mcanet/knitic/pcb_design/ArduinoDue_2.0_power_jumper_Vin_Arduino/KniticV201_+CompactPCB2Res_etch_silk_bottom.pdf

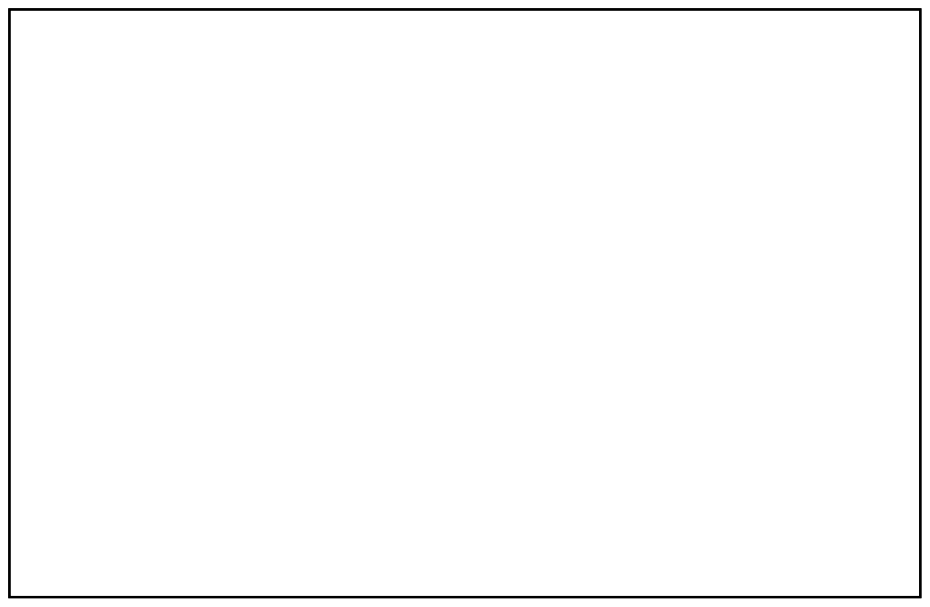
[picture p16: page 1]
