mcanet/knitic/pcb_design/ArduinoDue_2.0_power_jumper_Vin_Arduino/KniticV201_+CompactPCB2Res_etch_silk_bottom_mirror.pdf

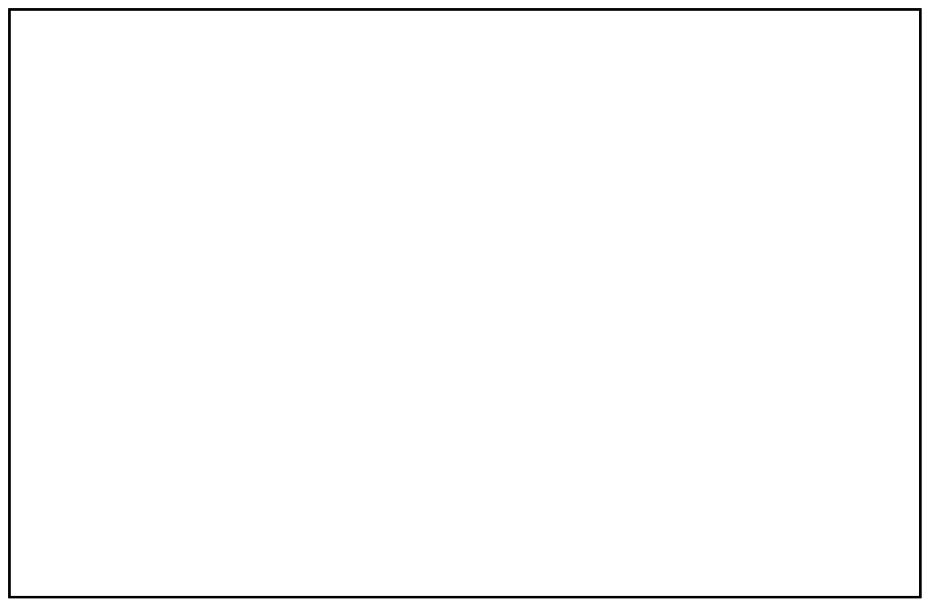
[picture p17: page 1]
