mcanet/knitic/pcb_design/ArduinoDue_2.0_power_jumper_Vin_Arduino/KniticV201_+CompactPCB2Res_etch_silk_top.pdf

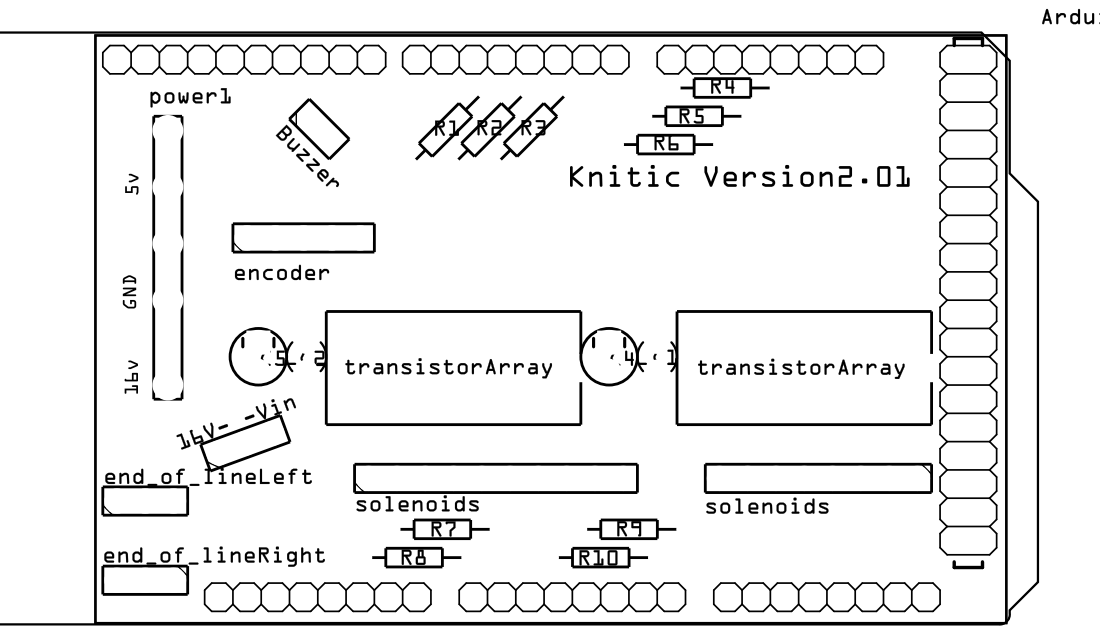
[picture p18: page 1]
