mcanet/knitic/pcb_design/ArduinoUno/KniticV1_pcb.pdf

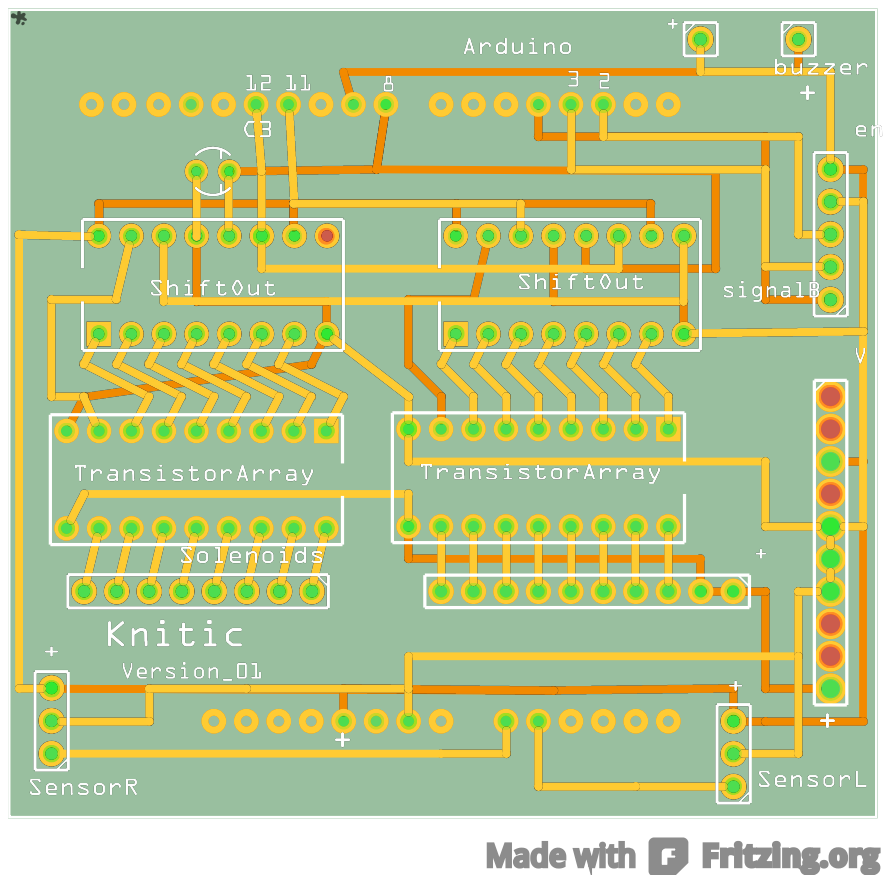
[picture p20: page 1]
