mcanet/knitic/arduino_code/openKnitting_handMadepcb_v0_1/communication.h

#ifndef COMMUNICATION_H_
#define COMMUNICATION_H_

#include "arduino.h"

#include "encoders.h"
#include "solenoids.h"
#include "endLines.h"

class communication {
  private:
    encoders* myEncoders;
    endLines* myEndlines;
    solenoids* mysolenoids;
    unsigned long lastSendTimeStamp;
    unsigned long lastRecieveTimeStamp;
    char receivedBin[202];
    int dataSize;
    boolean dataReplace;
    byte footer;
    char lf;
    boolean solenoidsAreOff;
    boolean corruptMessage;
    
  public:
    String _status;
    communication() {
    }
    ~communication() {
    }

    void setup(encoders* _myEncoders, endLines* _myEndlines, solenoids* _mysolenoids) {
      myEncoders = _myEncoders;
      myEndlines = _myEndlines;
      mysolenoids = _mysolenoids;
      lastSendTimeStamp = millis();
      lastRecieveTimeStamp = millis();
      dataSize = 202;
      footer = '&';
      dataReplace = false;
      solenoidsAreOff = false;
      corruptMessage = false;
      lf = '@';    // AT in ASCII
      Serial.setTimeout(10);
    }

    // send data to processing
    void sendSerialToComputer() {
      if ( (myEncoders->lastencoder1Pos != myEncoders->encoder1Pos)  || (millis() - lastSendTimeStamp) > 500 ) {
        lastSendTimeStamp = millis();
        Serial.print(",");
        Serial.print(myEncoders->stitch);
        Serial.print(",");
        Serial.print(myEncoders->headDirection);
        Serial.print(",");
        if (myEndlines->phase) {
          Serial.print("1");
        } else {
          Serial.print("0");
        }
        /*myEncoders->last_8segmentEncoder
        myEncoders->_8segmentEncoder
        if(myEncoders->last_8segmentEncoder){
          Serial.print("1");
        }else{
          Serial.print("0");
        }
        if(myEncoders->_8segmentEncoder){
          Serial.print("1");
        }else{
          Serial.print("0");
        }
        Serial.print(",");
        if(myEndlines->started){
          Serial.print("1");
        }else{
          Serial.print("0");
        }
        Serial.print(",");
        Serial.print(_status);
        Serial.print(",");
        for(int i=0;i<16;i++){
          if(mysolenoids->solenoidstateOn[i]){
            Serial.print("1");
          }else{
            Serial.print("0");
          }
        }
        Serial.print(",");
        Serial.print(myEncoders->encoder1Pos);
        Serial.print(",");
        Serial.print(mysolenoids->currentStitchSetup );
        Serial.print(",");
        Serial.print(mysolenoids->currentPixState);
        Serial.print(",");
        Serial.print(myEndlines->valueEndLineLeft);
        Serial.print(",");
        Serial.print(myEndlines->valueEndLineRight);
        Serial.print(",");
        Serial.print(myEncoders->directionEncoders);
        Serial.print(",");
        Serial.print(myEncoders->lastDirectionEncoders);
        */
        Serial.println(lf);
        myEncoders->lastencoder1Pos = myEncoders->encoder1Pos;
      }
      if (corruptMessage){
        Serial.print("C"); // for corrupt
        Serial.println(lf);
        corruptMessage=false;
      }
    }

    // recieve from processing
    void receiveAllLine() {
      while(Serial.available()) {
        if ( Serial.readBytesUntil(footer, receivedBin, dataSize)) {
          if (receivedBin[0]==lf){ // begin and end are here so ok
            dataReplace = true;
          }
          else{
            corruptMessage=true;
            sendSerialToComputer();
          }
        }
      }
      if (dataReplace) {
        lastRecieveTimeStamp = millis();
        sendCurrentPixelArray();
        dataReplace = false;
        solenoidsAreOff=false;
      }
      else if (((millis() - lastRecieveTimeStamp) > 50000) && (solenoidsAreOff==false)){ // release solenoid if nothing recieve after 50s
        mysolenoids->setAllSolOff();
        solenoidsAreOff=true;
      }
      
    }
    
    // send to processing
    void sendCurrentPixelArray() {
      Serial.println(lf);
      for (int i = 1; i < 201; i++) {
        pixelBin[i] = receivedBin[i];
        Serial.print(pixelBin[i]);
      }
      Serial.println(lf);
    }
};

#endif
