mcanet/knitic/protoAppKnitic_p5_3/editImage.pde

void showCursorPosition() {
  if ( mouseX>buttonWithBar && mouseX<(width-buttonWithBar) ) {
    patternMouseX = cols -(((mouseX-buttonWithBar)/sizePixel)-(100-leftStick))-1 ;
    patternMouseY = (mouseY/sizePixel)-(27-rows)+current_row+1;
  }
}

void mouseReleased() {
  try {
    if (editPixels) {
      println(pixelArray[patternMouseX][patternMouseY]);
      if (pixelArray[patternMouseX][patternMouseY]==0 ) {
        pixelArray[patternMouseX][patternMouseY]=1;
      }
      else {
        pixelArray[patternMouseX][patternMouseY]=0;
      }
      // pass to image
      img.loadPixels();
      int loc = patternMouseX + patternMouseY*img.width;
      if (pixelArray[patternMouseX][patternMouseY]==0) {
        img.pixels[loc] = color(0, 0, 0);
      }
      else {
        img.pixels[loc] = color(255, 255, 255);
      }
      img.updatePixels();
    }
  }
  catch(Exception e) {
  }
}
